specs32/catlight/catlight_MK2/arduino/04_CL/04_CL_LOG.ino

/**
 * Made with Marlin Bitmap Converter
 * https://marlinfw.org/tools/u8glib/converter.html
 *
 * This bitmap from the file 'lisa_djinn_logo_2.png'
 */
//#pragma once

#define LOGO_BMPWIDTH  32

const unsigned char bitmap_logo[] PROGMEM = {
  B00000000,B00000000,B00000000,B00000000, // ................................
  B00000000,B00000000,B00000000,B00000000, // ................................
  B00000000,B11111111,B11110000,B00000000, // ........############............
  B00000110,B11111110,B11111111,B00000000, // .....##.#######.########........
  B00001110,B01111100,B01111111,B11100000, // ....###..#####...##########.....
  B00011100,B00011000,B01111111,B11110000, // ...###.....##....###########....
  B00111110,B00000000,B00111111,B11111100, // ..#####...........############..
  B01111110,B00000000,B00110011,B11101100, // .######...........##..#####.##..
  B01110100,B00000000,B00100011,B00110110, // .###.#............#...##..##.##.
  B01100100,B01000110,B00100010,B00010010, // .##..#...#...##...#...#....#..#.
  B01001100,B11000110,B00000010,B00011011, // .#..##..##...##.......#....##.##
  B11001100,B01000010,B00000010,B00011011, // ##..##...#....#.......#....##.##
  B11001100,B00000001,B10000110,B00001110, // ##..##.........##....##.....###.
  B01101100,B00000001,B00000110,B00001110, // .##.##.........#.....##.....###.
  B00100011,B00000110,B00001100,B00001100, // ..#...##.....##.....##......##..
  B00111011,B11111100,B00111000,B00011100, // ..###.########....###......###..
  B00011111,B11110000,B01110000,B00111000, // ...#########.....###......###...
  B00000111,B11000000,B11100000,B01110000, // .....#####......###......###....
  B00000000,B00000011,B11000001,B11100000, // ..............####.....####.....
  B00000000,B00001111,B00000011,B10000000, // ............####......###.......
  B00000000,B11111110,B01111110,B00000000, // ........#######..######.........
  B11111111,B11111111,B11111000,B00000000, // #####################...........
  B11111111,B11111111,B10000000,B00000000, // #################...............
  B00000000,B00000000,B00000000,B00000000  // ................................
};
